ar3misByte/bleep/Sensora_Novelty_Analysis.docx

SENSORA

Novelty & Differentiation Analysis

How this project differs from existing worker-safety, disaster-communication, and hazard-detection systems

Prepared 16 September 2026

# 1. Methodology

The 22 novelty points below are benchmarked against specific existing academic and applied systems identified through a literature and product review spanning the project's five source domains: smart worker-safety monitoring, disaster-resilient emergency communication, embedded smart helmets, intelligent fire/gas hazard detection, and flash-flood early warning. Four systems were reviewed in enough depth to ground direct comparisons (full citations in Section 4); several additional sources are listed as further reading. Each novelty claim below names the specific limitation or gap it addresses, so it can be checked rather than taken on faith — and so it can be defended the same way in front of a judge.

# 2. At a Glance

Dimension | Typical existing systems (reviewed) | Sensora
Domain coverage | One hazard type per system — helmet, fire/gas, flood and comms are separate research threads | One architecture unifying worker, environmental, and network-health monitoring
Dependency for intelligence | Fall/heat/gas logic runs after data reaches the cloud (Firebase/Blynk); "if Wi-Fi fails, the intelligence of the system often fails" | Safety state is computed and acted on (buzzer/LED) at the edge, before any packet is sent
Routing under node failure | Not addressed, or a single fixed protocol whose delivery rate degrades with hop count (85%→72% over 3→5 hops) | Hybrid: efficient routing for routine data, TTL-bounded flooding that guarantees delivery for emergencies
Traffic prioritization | Undifferentiated — all messages treated the same | Explicit priority field; CRITICAL/SOS traffic always multi-path flooded
Cross-hazard interoperability | Each hazard type has its own device, protocol, and dashboard | One packet format and one mesh shared by helmet, relay, and environmental nodes
AI on the safety-critical path | Bare threshold (accel > 2.5g) or opaque deep models (LSTM/YOLO) with no interpretability discussion | Deterministic, explainable edge logic for worker state; ML reserved for the one genuinely uncertain estimate (flood risk), clearly labeled
Real vs. simulated data | Simulated/validation data used without an architecturally separate, clearly labeled path | Real and simulated data enter through the identical ingestion pipeline and are tagged at the packet level
Network health visibility | Communication treated as plumbing — not surfaced as monitored data | Node status and route changes are first-class database entities and dashboard timeline events
Security | Not discussed in any of the five reviewed systems | Replay protection is built into the routing design; per-node authentication is named as a planned addition

# 3. The 22 Novelty Points

## A. Cross-domain system integration (not five projects glued together)

N1. One packet format across every hazard type

Existing approach: Existing systems each define their own sensor set and message schema; none of the reviewed helmet, fire/gas, or flood systems share a wire format across worker, environmental, and network-health data.

Sensora's novelty: Sensora defines a single binary packet schema (version / type / source / sequence / TTL / hop count / priority / payload) used identically by helmet, relay, and environmental nodes — a flood alert and a worker SOS are structurally the same kind of message, differing only in payload.

N2. A single command view spans three domains

Existing approach: Reviewed dashboards are domain-siloed: Firebase for the helmet, Blynk for fire/gas, Grafana for the flood system — three separate integrations, three separate screens.

Sensora's novelty: Sensora's dashboard shows worker status, network topology, and environmental risk on one screen, because they are one data model, not three bolted-on integrations.

N3. Emergency semantics are shared, not duplicated

Existing approach: Each reviewed system invents its own alert schema and channel (email via MailerSend, push via Blynk, LINE messages via Node-RED).

Sensora's novelty: The worker risk engine and the flood engine both emit the same {hazardType, severity} structure into the same event table and the same priority-flood transport — hazard classification is one shared contract.

N4. Network health is treated as safety telemetry, not plumbing

Existing approach: None of the reviewed systems log node-up/down or route-change events as part of the safety narrative.

Sensora's novelty: Sensora's network_events table and dashboard timeline narrate the network's own resilience alongside worker and environmental events — “the network survived” is as visible a fact as “the worker is safe.”

## B. Communication resilience (the most literature-differentiated area)

N5. Safety state survives total loss of connectivity

Existing approach: The reviewed smart-helmet paper states its design “assumes continuous Wi-Fi connectivity” with “no offline data buffering or edge-computing failover,” and would fail silently without it.

Sensora's novelty: Sensora's edge rule engine drives the local buzzer/LED before any packet is sent — the helmet is safe on its own; the mesh is an added layer, not a dependency.

N6. Priority-aware routing, not uniform routing

Existing approach: The reviewed LoRa mesh network (AODV-derived) reports delivery success falling from 85% at 3 hops to 72% at 5 hops, with no message-class prioritization.

Sensora's novelty: Sensora routes routine telemetry efficiently via distance-vector, but trades airtime for guaranteed multi-path delivery — TTL-bounded flooding — specifically for CRITICAL/SOS traffic.

N7. Deterministic, demo-verifiable failure recovery

Existing approach: The same LoRa mesh study reports aggregate delivery statistics but no live, on-demand failure/recovery demonstration.

Sensora's novelty: Sensora's heartbeat-timeout mechanism (~9s to reroute) is designed to be triggered on command: power off a specific relay and watch detection → reroute → delivery happen on the dashboard — a repeatable demonstration, not just a statistic.

N8. Communication carries sensing, not just location and text

Existing approach: The reviewed LoRa emergency network carries “text messaging only” and GPS, with, by the authors' own statement, “no worker health or hazard detection sensors integrated.”

Sensora's novelty: Sensora's mesh is the same transport used for multi-sensor worker telemetry, emergency packets, and environmental data — sensing and communication were designed together, not layered afterward.

N9. Replay/spoofing resistance considered even at hackathon scope

Existing approach: None of the five reviewed systems mention authentication, replay, or spoofing protection at any layer.

Sensora's novelty: Sequence-number-based replay rejection (needed anyway for flood dedup) and a planned per-node HMAC tag make security a stated design element rather than an unaddressed gap.

## C. Edge intelligence and sensor fusion

N10. Fall detection with context, not a bare threshold

Existing approach: The reviewed helmet paper's fall logic is a fixed accelerometer/deceleration threshold (2.5g → <0.5g within 500ms); its own authors note it cannot distinguish a fall from a jump.

Sensora's novelty: Sensora requires an impact spike followed by a subsequent lack of motion before declaring CRITICAL — aimed directly at that named limitation.

N11. Weighted multi-signal fusion, not single-sensor triggers

Existing approach: The same helmet paper states plainly that “no multi-sensor fusion algorithms exist” in its design.

Sensora's novelty: Sensora's edge risk score deliberately combines temperature, gas deviation, and motion into one fused state, with SOS as a hard override — fusion is the mechanism, not a stated absence.

N12. Interpretable-by-design safety logic

Existing approach: The reviewed flash-flood system's core classifiers are an LSTM network and a YOLO detector — accurate, but neither paper discusses interpretability or an explicit false-alarm control.

Sensora's novelty: Sensora keeps the safety-critical edge path to a transparent, auditable rule/weighted-score engine, and reserves statistical modeling for the one signal (flood risk) where it is genuinely justified — an argued trade-off, not a default “deep-learn-everything” approach.

N13. Fleet-level correlation, not just per-device thresholds

Existing approach: Every reviewed worker-safety and fire/gas system evaluates one device against its own thresholds only.

Sensora's novelty: Sensora's backend anomaly layer looks across the current worker fleet for simultaneous elevated readings — a site-wide pattern no single edge device can see by construction, and a capability absent from all five reviewed systems.

## D. Data and methodology honesty

N14. Simulated and real data share one pipeline, by architecture

Existing approach: The reviewed flood system trains and validates against site data without describing an explicit real/simulated separation; its own accuracy varies sharply between sites (R² of 0.987 vs. 0.781), a sensitivity the architecture doesn't call out.

Sensora's novelty: Sensora routes real sensor readings and synthetic scenario data through the identical MQTT topics and risk engine, so “simulated” is a labeled data source, not a different code path that could behave differently in front of judges than in the field.

N15. A physically-manipulable, honestly-labeled hybrid demo signal

Existing approach: Every reviewed system is either fully real (deployed sensors) or fully synthetic (a dataset) — none blend the two at the hardware level for a live audience.

Sensora's novelty: Sensora's flood node pairs a real ultrasonic water-level reading with a presenter-turned potentiometer standing in for rainfall intensity, tagged as simulated in the packet itself — tangible and transparent at the same time.

N16. Named limitations with stated mitigations, not buried future-work

Existing approach: The reviewed papers disclose limitations (Wi-Fi dependency, GPS drift, short battery life) primarily in discussion or future-work sections, after the results.

Sensora's novelty: Sensora's design carries a standing, pre-emptive list of exactly what is cut and why (gas sensor calibration, GPS reliability, mesh security), each paired with its real-world fix — a documentation discipline, not only an engineering one.

## E. Hardware and demo engineering

N17. GPS-optional-by-design location fallback

Existing approach: The reviewed helmet paper relies on live GPS lock (3–5m accuracy) without addressing indoor dead zones — a known failure mode for any indoor demo.

Sensora's novelty: Sensora treats GPS as a deployment-time field in the packet schema while using fixed zone labels for the actual demo, avoiding a live dependency on satellite acquisition that no reviewed system accounts for.

N18. Power budget stated as a number, not omitted

Existing approach: Only one reviewed system (the LoRa mesh network) quantifies battery life (~72h without solar); none of the worker-safety or hazard-detection papers give a comparable figure.

Sensora's novelty: Sensora states an explicit estimate (8–12h on a 2000mAh LiPo at measured draw), so the team can answer a judge's power question with a number rather than an assurance.

N19. Node role, not node type, defines the firmware

Existing approach: Reviewed systems build a distinct device per hazard type — a helmet device, a separate fire/gas node, a separate flood station.

Sensora's novelty: Sensora's relay, helmet, environmental, and gateway nodes run variants of the same mesh firmware differentiated by a role flag — cheaper to build, and it is exactly what lets a bare relay (no sensors at all) participate in, and be killed for, the reroute demo.

## F. Engineering process as a differentiator

N20. Architecture explicitly optimized for live verifiability

Existing approach: The reviewed research systems report offline metrics — precision, mAP, R², delivery percentage — as their measure of success.

Sensora's novelty: Sensora's specific choices (the ~9s reroute window, a fixed-layout topology view mirroring the physical table, a scripted kill-a-node moment) are chosen because they must be demonstrated correctly, once, live, in front of judges — a different and arguably harder constraint than a lab benchmark.

N21. Judge-anticipation built into the design record itself

Existing approach: None of the reviewed papers structure their limitations as anticipated third-party questions.

Sensora's novelty: Sensora's architecture document includes a standing “what a judge will challenge” section, answered in advance — critical scrutiny is a design input, not a Q&A afterthought.

N22. One narrative, five demos, shared infrastructure

Existing approach: The five source problem statements (worker safety monitoring, disaster-resilient comms, smart helmet, fire/hazard detection, flash-flood warning) are, in the reviewed literature, pursued as five unrelated research threads by different groups.

Sensora's novelty: Sensora's core claim — the same edge-to-mesh-to-dashboard chain carries a worker's fall, a relay's death, and a river's rise — is the product of treating those five problems as one distributed system from the first design decision, not a restated feature list.

# 4. References

## Sources reviewed in depth

• Developing an IoT-Enabled Smart Helmet for Worker Safety: Technical Feasibility and Business Model — https://www.mdpi.com/2313-576X/11/3/89 (source for helmet sensor set, cloud dependency, and fall-detection limitations cited in points A–C)

• Intelligent IoT-Based Fire and Gas Leakage Detection System: Integrating Sensor Fusion, Edge AI, and Visual Verification — https://www.ijert.org/intelligent-iot-based-fire-and-gas-leakage-detection-system-integrating-sensor-fusion-edge-ai-and-visual-verification-ijertv15is041584 (source for fire/gas edge-AI approach and stated network-dependency limitation)

• Solar-Powered LoRa Mesh Network for Emergency Communication and Tracking During Disasters — https://ijarcce.com/wp-content/uploads/2025/12/IJARCCE.2025.141266-Solar.pdf (source for LoRa mesh routing/delivery statistics and scope (text + GPS only, no hazard sensing))

• Development of an AIoT-Based Early Flash-Flood Warning System for Smart Rural Disaster Resilience — https://www.mdpi.com/1424-8220/26/11/3512 (source for flood-system sensor stack, YOLOv10/LSTM approach, and lack of cross-hazard integration)

## Further reading (identified, not individually cited above)

- An IoT-Enabled Smart Safety Helmet for Enhancing Worker Protection on Construction Sites — ResearchGate
- Toward intelligent construction safety: a systematic review of IMU-based fall-from-height detection — ScienceDirect
- Review: Wearable sensing devices for construction safety — ScienceDirect
- A literature review: rainfall thresholds as flash-flood monitoring for an early warning system — IWA Publishing
- LoRa-based Mesh Network for Off-grid Emergency Communications — ResearchGate
- Wireless Sensor Network Application for Fire Hazard Detection and Monitoring — Springer

This document should be read alongside the project's System Architecture Plan, which sets out how each of these novelty points is actually implemented within the 36–48-hour build.
